gmoccapy/T4-MFA/Fotos/20260506_101403.jpg

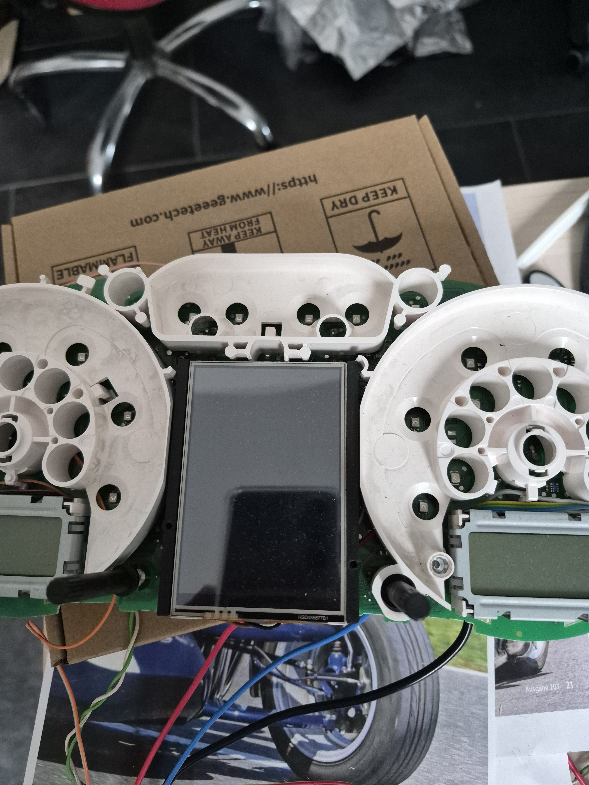
Fotos/20260506_101403.jpg
