gmoccapy/T4-MFA/Fotos/20260506_101413.jpg

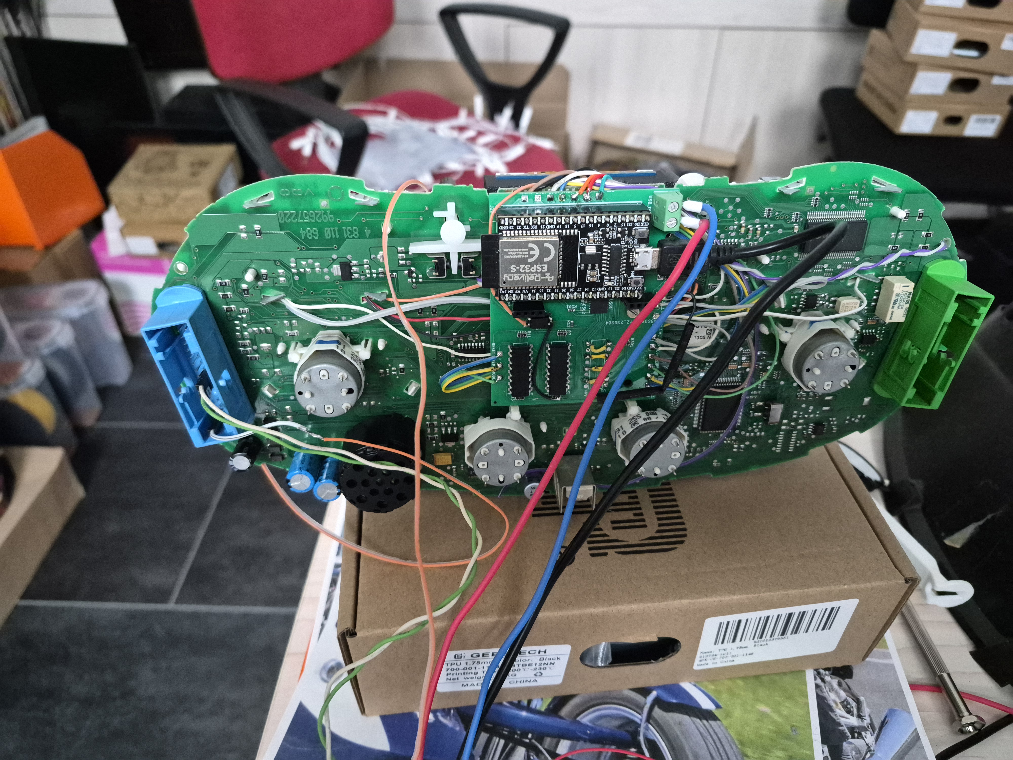
Fotos/20260506_101413.jpg
