gmoccapy/T4-MFA/Fotos/Housing_Power_Suply _ 2.jpg

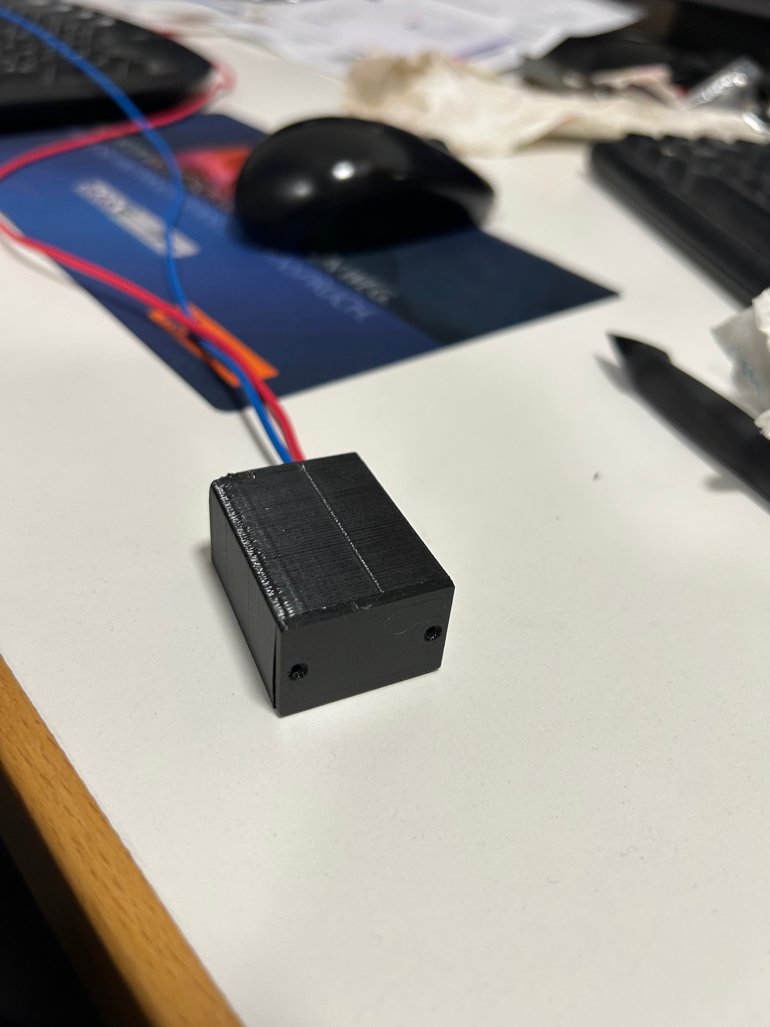
Fotos/Housing_Power_Suply _ 2.jpg
