gmoccapy/T4-MFA/Fotos/Modification_Back_cover_1.jpg

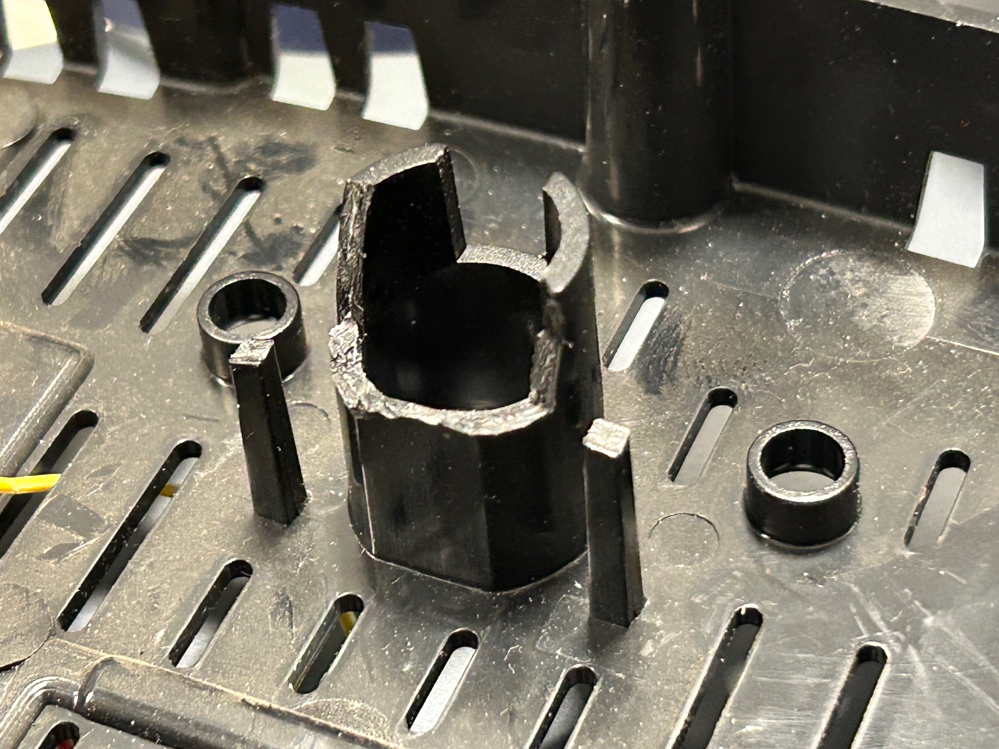
Fotos/Modification_Back_cover_1.jpg
