gmoccapy/T4-MFA/Daniels_Code/MFA_TFT_25012026/update_values.ino

void update_GPS(void) {
    while (GPS_Serial.available() > 0) {
    gps.encode(GPS_Serial.read());
  }
  // gültiges Signal?
  if (gps.location.isValid() && gps.date.isValid() && gps.time.isValid()) {
    _GPS_valid = true;
    
    int hour = gps.time.hour() + _GPS_timezone_offset;
    if (hour >= 24) hour -= 24;
    if (hour < 0) hour += 24;
    _GPS_time = hour * 3600UL + gps.time.minute() * 60UL + gps.time.second();

    _GPS_direction = gps.course.deg();  // 0-360
    _GPS_speed = gps.speed.kmph();
    _GPS_last_update = millis();
    _GPS_altitude = gps.altitude.meters();
  }

  // Timeout: >10 Sekunden dann ungültig
  if (millis() - _GPS_last_update > 10000) {
    _GPS_valid = false;
  }
}

void update_time(void){
  if (motor_on) {         // Zeit für durchschnittsgeschwindigkeit soll nur zählen wenn der Motor läuft
  Data.time_start += ((millis() - lastMillis)) / 1000;
  lastMillis = millis();

 //if (_GPS_valid) {        // GPS Uhrzeit macht hier keinen Sinn, da nur die Zeit genommen werden sollte, wenn der Motor läuft
 //   Data.time_start = _GPS_time;  // Sek. seit Mitternacht
 //   time_last = Data.time_start;
 // }
  // Minuten Logik
  if((Data.time_start - time_last) > 59){
    Data.time_refuel += 1;
    Data.time_long_period += 1;
    time_last = Data.time_start;
  }
  }
  
// DEBUG  
  if(temp_page == 6){
    tft.setTextDatum(MC_DATUM);
   // tft.fillScreen(TFT_BLACK);
    temp = (shutdown_timer + shutdown_time - millis()) / 1000 ;
    dtostrf(temp, 4, 0, TFT_String);
    draw_value_box(250, 134, 50, TFT_String);
  }
}


void update_volt(void){
  // Get the Voltage value from PIN 4 from ESP32 coresponds to ADC1_CH3
  temp = analogRead(PIN_Volt);      
if (temp > 1500) {  // K15 = Zündung an
  ignition_on = true;
} else {
  ignition_on = false;
}

  // Check if over or undervoltage, to turn on the LED

#ifdef SYM_NA_VISIBLE
//kein Batterie Symbol im Display, Batterie wird über getrennte LED im Kombiinstrument angezeigt
#else
if((temp > 4000) || (temp < 1800)){
//    Serial.println(temp);
    if (battery == false) {
      battery = true;
      check_led = true;
    }
  }
  else if(battery == true) {
    battery = false;
    check_led = true;
  }
#endif

  // ignition is on! K15 with 12 V
  if (temp > 1500){
    // ignition came back bevor shut down timer expired, so reset timer
    // and redraw page, as we have blanked it out loosing K15
    if (shutdown_timer != 0){
      shutdown_timer = 0;
      if (temp_page != Data.page){
        temp_page = Data.page;
        DrawSelected(Data.page);
      }
    }
    // if we had an power off, we need to put Hold high
    if (digitalRead(PIN_STAY_ON) == false){
      digitalWrite(PIN_STAY_ON, 1);
    }
  }
  // no Current on K15, so switch off display (better sayed just draw black screen)
  else{
    volt = temp;
    if (motor_on == false){
      if ((shutdown_timer == 0) && (digitalRead(PIN_STAY_ON) == true)){
        shutdown_timer = millis();
        check_led = false;  // otherwise we will have symbols displayed on off page     zusatzprüfung in check_led eingefügt
       temp_page = 6;
       DrawSelected(temp_page);
      }
    }
  }
  // get rid of noise influence ; high pass filtering 
  // take 90% of old value and 10% of new value to smooth the display
  volt = (0.9 * volt) + (0.1 * temp);
}

void update_values(void){
  // max 6 info lines
  // Line 1 = 72
  // Line 2 = 138
  // Line 3 = 204
  // Line 4 = 270
  // Line 5 = 337
  // Line 6 = 404

//DEBUG:
//Serial.println("This is update values");

  tft.setTextDatum(MR_DATUM); // middle right

  // to avoid update values for warnings in full page mode
  if (Data.page == temp_page){
    // Shutdown-Seite (6) unabhängig vom Memory
    if (temp_page == 6) {
      // DEBUG: Countdown aktualisieren
      temp = (shutdown_timer + shutdown_time - millis()) / 1000;
      dtostrf(temp, 4, 0, TFT_String);
      draw_value_box(250, 134, 50, TFT_String);
      return;
    }}

    
    if (currentMemory == 0) {
      switch(Data.page) {
        case 0:
        
          draw_value_cruise_control(70);
          draw_compass(105, 70);
          draw_value_average_consumption(316, Data.mode);
          draw_value_range(372);
          draw_value_out_temp(428);
          // draw oil temp scale
          draw_bar("Oil", "`C", 15, 115, temp_oil, 0, 160, 60, 130, 140);
          // draw volt scale
          draw_bar("V", "V", 269, 115, volt * VOLT_FAKTOR, 0, 18, 11, 15, -1);
          
      #ifdef with_DIAL
      //Serial.println(warnings); 
      if ( (motor_on == false) || (battery)  ){ //    || (warnings)      WARNINGS muss noch geprüftwerden
        // do nothing
      }
      else{
        // draw_dial needs 181 pixel hight, value may be changes with #define SPRITESIZE and SPRITEPIVOT
        switch(Data.mode){

          case START:  
            // C_last_25_km = 1755.65 ml/25km = 70.226 ml/km => 0,070226 l/km = 7.0226 l/100km 
            if (Data.km_start > 0 ){
              // temp = C_last_25_km / 250.0;  // ml/25 km and 100km gives factor 250   
              temp = (Data.C_start / float(Data.km_start)) / 10.0 ; // 1000 ml/l and 100 km gives factor 10
            }
            else{
              temp = 0.0;
            }
              draw_dial(75, 108, temp, 1, C_dial_display_value, 24.0, F("seit"), F("Start"));
            break;

          case REFUEL:
            if (Data.km_start > 0 ){
              temp = (Data.C_refuel / float(Data.km_refuel)) / 10.0 ; // 1000 ml/l and 100 km gives factor 10
            }
            else{
              temp = 0.0;
            }
            draw_dial(75, 108, temp, 1, C_dial_display_value, 24.0, F("seit"), F("Tanken"));
            break;

          case PERIOD:
            if (Data.km_start > 0 ){
              temp = (Data.C_long_period / float(Data.km_long_period)) * 100.0; // l / km *100
            }
            else{
              temp = 0.0;
            }
            draw_dial(75, 108, temp, 1, C_dial_display_value, 24.0, F(""), F("Langzeit"));
            break;
        }
      }
    #endif      



          break;

        case 1:
          draw_value_trip(72,Data.mode);
          draw_value_actual_consumption(138);
          draw_value_deposit(204);
          draw_value_average_consumption(270, Data.mode);
          draw_value_time(337, Data.mode);
          draw_value_average_velocity(404, Data.mode);
          break;

        default:
          break;
      }
    } else {  // Memory == 1
      switch(Data.page) {
        case 0:
   
          break;

        case 1:
      
      draw_value_cruise_control(70);
      draw_compass(105, 70);

      draw_GPS_altitude(70+64);
      draw_GPS_direction(70 + 109); 
      draw_GPS_time(70 + 154);       // Zeile 7
      draw_GPS_speed(70 + 200); 
      draw_value_UMin(337);
      draw_value_oil_temp(404);  
                  
          break;

        default:
          break;
      }
    }
  
}


void clearUnitsArea(int Y_Pos) {    // Bereich löschen zur Umschaltung Verbrauch l/h auf l/100km und zurück

  int h = tft.fontHeight(FONT4);

  int maxWidth = max(
    tft.textWidth(HUNDERTKM, FONT4),
    tft.textWidth(HOUR, FONT4)
  );

  tft.fillRect(
    230,         
    Y_Pos - h,
    maxWidth,
    2 * h,
    BACK_COLOR
  );
}
/*
void draw_value_actual_consumption(int Y_Pos){
  float temp = 0.0;
  // Einheiten dynamisch wechseln: l/h ↔ l/100km
  if (velocity_actual < 5.0) {
    if (units_l_100_km == true) {
      clearUnitsArea(Y_Pos);
      drawUnits(Y_Pos, LITER, HOUR);
      units_l_100_km = false;
    }
    // Stand: zeige l/h
    temp = C_actual_l_per_h;
  } else {
    if (units_l_100_km == false) {
      clearUnitsArea(Y_Pos);
      drawUnits(Y_Pos, LITER, HUNDERTKM);
      units_l_100_km = true;
    }
    // Fahrt: zeige l/100km
    temp = C_actual_l_per_100km;
  }
 
  if (temp > 99.9) temp = 99.9;
  if (temp < 0) temp = 0.0;

  dtostrf(temp, 4, 1, TFT_String);
  draw_value_box(Y_Pos, 134, 50, TFT_String);
}
*/

void draw_value_actual_consumption(int Y_Pos)
{
  float value;

  if (velocity_actual < 5.0f) {
    // l/h
    value = C_actual_l_per_h;
    if (!unit_l_hour) {
      clearUnitsArea(Y_Pos);
      unit_l_hour = true;
    }
    drawUnits(Y_Pos, LITER, HOUR);
  } 
  else {
    // l/100km
    value = C_actual_l_per_100km;
    if (unit_l_hour) {
      clearUnitsArea(Y_Pos);
      unit_l_hour = false;
      }
      drawUnits(Y_Pos, LITER, HUNDERTKM);
  }

  if (value < 0.0f)  value = 0.0f;
  if (value > 99.9f) value = 99.9f;

  dtostrf(value, 4, 1, TFT_String);
  draw_value_box(Y_Pos, 134, 50, TFT_String);
}


void draw_value_time(int Y_Pos, int _case){
  switch(_case){

    case START: // time from start in sec
      temp = Data.time_start;
      break;

    case REFUEL: // time since refuel in min
      temp = Data.time_refuel * 60;
      break;

    case PERIOD: // time long period in min
      temp = Data.time_long_period * 60;
      break;
  }

    // check if we are over 99 hours and 59 minutes
    // if so we have to strip minutes due to space reasons
    if(temp <= 359940){
      char hours[3];
      dtostrf((int(temp) / 3600), 2, 0, hours);
      char minutes[3];
      dtostrf((int(temp) / 60) % 60, 2, 0, minutes);
      // fill with leading zeros
      for(int i = 0; i < strlen(minutes); i++){
        if(minutes[i] == ' '){
          minutes[i] = '0';
        }
        else{
          break;
        }
      }
      strcpy(TFT_String, hours);
      strcat(TFT_String, ":");
      strcat(TFT_String, minutes);
    }
    else{
      dtostrf((int(temp) / 3600), 5, 0, TFT_String);
    } 
    draw_value_box(Y_Pos, 145, 50, TFT_String);
}

void draw_value_trip(int Y_Pos, int _case){
    
    switch(_case){

    case START: // trip from start
      dtostrf(Data.km_start, 3, 0, TFT_String);
      break;
      
    case REFUEL: // trip since refuel
      dtostrf(Data.km_refuel, 3, 0, TFT_String);
      break;
  
    case PERIOD: // trip since refuel
      dtostrf(Data.km_long_period, 6, 0, TFT_String);
      break;
    }
  draw_value_box(Y_Pos, 134, 50, TFT_String);
}

void draw_value_consumption(int Y_Pos, int _case){
  
  switch(_case){

    case START: // consumption from start
      if(Data.C_start > 0){
        // C_from_start = 500 ml  
        temp = Data.C_start / 1000.0; // 1000ml / 1l
        dtostrf(temp, 4, 1, TFT_String);
      }
      else{
        String(F("--.-")).toCharArray(TFT_String, 5);
      }  
      break;

    case REFUEL: // consumption since refuel
      if(Data.C_refuel > 0){
        // C_refuel = 500 ml 
        temp = Data.C_refuel / 1000.0; // 1000ml / 1l
        dtostrf(temp, 4, 1, TFT_String);
      }
      else{
        String(F("--.-")).toCharArray(TFT_String, 5);
      }  
      break;

    case PERIOD: // consumption long period
      if(Data.C_long_period > 0){
        // C_long_period = 86.38 l and km_long_oeriod = 1234 km => 86.38 l * 100.0 km / (1234 km) = 86.38 l / (1234 / 100) km 
        temp = Data.C_long_period; // l
        dtostrf(temp, 4, 1, TFT_String);
      }
      else{
        String(F("--.-")).toCharArray(TFT_String, 5);
      }
      break;  
  }
  draw_value_box(Y_Pos, 134, 50, TFT_String);
}

void draw_value_average_consumption(int Y_Pos, int _case){
  
  switch(_case){

    case START: // average consumption from start
      if(Data.km_start > 0){
        // C_start = 2100 ml and km_start = 35 km => 2100 ml / 35 km => 60 ml / 1 km => 6000 ml / 100 km => 6,0 l / 100 km 
        temp = (Data.C_start / float(Data.km_start)) / 10.0 ; // 1000 ml/l and 100 km gives factor 10
        dtostrf(temp, 4, 1, TFT_String);
      }
      else{
        String(F("--.-")).toCharArray(TFT_String, 5);
      }  
      break;

    case REFUEL: // average consumption since refuel
      if(Data.km_refuel > 0){
        // C_refuel = 2100 ml and km_refuel = 35 km => 2100 ml / 35 km => 60 ml / 1 km => 6000 ml / 100 km => 6,0 l / 100 km 
        temp = (Data.C_refuel / float(Data.km_refuel)) / 10.0 ; // 1000 ml/l and 100 km gives factor 10
        dtostrf(temp, 4, 1, TFT_String);
      }
      else{
        String(F("--.-")).toCharArray(TFT_String, 5);
      }  
      break;

    case PERIOD: // average consumption long period
      if(Data.km_long_period > 0){
        // C_period = 2.100 l and km_period = 35 km => 2.1 l / 35 km => 0.06 l/km => 6.0 l/100 km  
        temp = (Data.C_long_period / float(Data.km_long_period)) * 100.0; // l / km *100
        dtostrf(temp, 4, 1, TFT_String);
      }
      else{
        String(F("--.-")).toCharArray(TFT_String, 5);
      }
      break;  
  }
  draw_value_box(Y_Pos, 134, 50, TFT_String);
}

void draw_value_cruise_control(int Y_Pos){
  // cruise control
  uint color;
  if(velocity_cruise_control > 0){
    dtostrf(velocity_cruise_control, 3, 0, TFT_String);
    color = TFT_GREEN;
  }
  else{
    String(F("---")).toCharArray(TFT_String, 12);
    color = TEXT_COLOR;
  }  
  draw_value_box(Y_Pos, 95, 50, TFT_String); // value box von 134 auf 90 geändert wegen compass
  tft.drawXBitmap(19, Y_Pos - 25, sym_cruise_control, 50, 50, color);
}

void draw_value_average_velocity(int Y_Pos, int _case){
  
  switch(_case){

    case START: // average velocity from start
      if(Data.time_start > 0){
        // time_from_start in sec and km_from_start in km 
        temp = Data.km_start * 3600.0 / float(Data.time_start); 
        dtostrf(temp, 4, 0, TFT_String);
      }
      else{
        String(F("--.-")).toCharArray(TFT_String, 5);
      }  
      break;

    case REFUEL: // average velocity since refuel
      if(Data.time_refuel > 0){
        // km_refuel = 35 km and time_refuel = 57 min => 35 km / 57 min = 0,614 km/min => 0,614 * 60 min/h = 36.8 km/h 
        temp = Data.km_refuel * 60.0 / float(Data.time_refuel); 
        dtostrf(temp, 4, 1, TFT_String);
      }
      else{
        String(F("--.-")).toCharArray(TFT_String, 5);
      }  
      break;

    case PERIOD: // average velocity long period
      if(Data.time_long_period > 0){
        // km_period = 35 km and time_period = 57 min => 35 km / 57 min = 0,614 km/min => 0,614 * 60 min/h = 36.8 km/h 
        temp = Data.km_long_period * 60.0 / float(Data.time_long_period); 
        dtostrf(temp, 4, 1, TFT_String);
      }
      else{
        String(F("--.-")).toCharArray(TFT_String, 5);
      }  
      break;  
  }
  draw_value_box(Y_Pos, 134, 50, TFT_String);
}

void draw_value_oil_temp(int Y_Pos){
  if(temp_oil < 10){
    String(F("---")).toCharArray(TFT_String, 4);
  }
  else{
    dtostrf(temp_oil, 3, 0, TFT_String);
  }
  draw_value_box(Y_Pos, 134, 50, TFT_String);
}

void draw_value_volt(int Y_Pos){
  if(battery == true){
    check_led = true;
    String(F("---")).toCharArray(TFT_String, 4);
  }
  else{
    dtostrf(volt * VOLT_FAKTOR, 6, 1, TFT_String);
  }
  draw_value_box(Y_Pos, 134, 50, TFT_String);
}

void draw_value_out_temp(int Y_Pos){
  dtostrf(temp_out, 6, 1, TFT_String);
  draw_value_box(Y_Pos, 95, 50, TFT_String); //134

bool show_snowflake = (temp_out <= 4.0);

  if (show_snowflake != temp_out_warning) {
      // Hintergrund löschen (einmalig bei Wechsel)
        tft.fillRect(Icon_Pos_Snowflake[0], Icon_Pos_Snowflake[1], 50, 50, BACK_COLOR);
        temp_out_warning = show_snowflake;
  }
       if (show_snowflake) {
            tft.drawXBitmap(Icon_Pos_Snowflake[0], Icon_Pos_Snowflake[1], sym_snowflake, 50, 50, TEXT_COLOR);
        } else {
            tft.drawXBitmap(Icon_Pos_Snowflake[0], Icon_Pos_Snowflake[1], sym_temp2, 50, 50, TEXT_COLOR);
        }
      }

void draw_value_UMin(int Y_Pos){
  static float UMin_smooth = 0.0;
  UMin_smooth = 0.75f * UMin_smooth + 0.25f * UMin; 

  // Runden auf 20er Schritte
  int UMin_display = (int)(UMin_smooth + 10) / 20 * 20;

  if (UMin_display < 0) UMin_display = 0;
  if (UMin_display > 9990) UMin_display = 9990;

  static int last_UMin = -1;
  if (UMin_display != last_UMin) {
    last_UMin = UMin_display;
    dtostrf(UMin_display, 4, 0, TFT_String);
    draw_value_box(Y_Pos, 134, 50, TFT_String);
  }
}

void draw_value_deposit(int Y_Pos){
  dtostrf(deposit, 4, 0, TFT_String);
  draw_value_box(Y_Pos, 134, 50, TFT_String); 
}

void draw_value_range(int Y_Pos){

if (petrol || deposit <= 8) {
    tft.setTextColor(TFT_RED, BACK_COLOR);          
    strcpy(TFT_String, "---");
    draw_value_box(Y_Pos, 134, 50, TFT_String); 
    tft.setTextColor(TEXT_COLOR, BACK_COLOR);  
    return;
  }

  if (Data.km_refuel < 1 || C_last_25_km <= 0.0) {
    String(F("---")).toCharArray(TFT_String, 12);
    draw_value_box(Y_Pos, 134, 50, TFT_String);
    return;
  }

  float verbrauch_ml_pro_km = C_last_25_km / 25.0f;
  float tank_ml = deposit * 1000.0;
  temp = tank_ml / verbrauch_ml_pro_km;

  if (temp > 999) temp = 999;
  if (temp < 0) temp = 0;

  dtostrf(temp, 3, 0, TFT_String);
  draw_value_box(Y_Pos, 134, 50, TFT_String);
}

//Direkte Auswertung des öl level sensor scheint keine brauchbare lösung. besser über K-Line?

//void draw_value_oil_lvl(int Y_Pos) {

//  char buf[12];

//  if (oil_lvl_mm > 0.1f) {
//    dtostrf(oil_lvl_mm, 3, 1, buf);
//    strcat(buf, "mm");                          
  //  Serial.printf(">>> Ölstand: %s\n", buf);    
//  } else {
//    strcpy(buf, "---");
  //  Serial.println(">>> Ölstand: ---");
//  }

//  draw_value_box(Y_Pos, 134, 50, buf);
//}


void draw_GPS_time(int Y_Pos) {
  tft.setTextDatum(ML_DATUM);
  tft.drawString("Zeit", 14, Y_Pos, FONT4);

  if (_GPS_valid) {
    sprintf(TFT_String, "%02lu:%02lu:%02lu",
            _GPS_time / 3600,
            (_GPS_time % 3600) / 60,
            _GPS_time % 60);
  } else {
    strcpy(TFT_String, "!Signal");
  }
  draw_value_box(Y_Pos, 134, 50, TFT_String);
}

void updateDebug(void){
  // DEBUG
  // tft.setTextDatum(MR_DATUM);
  // dtostrf(bitValue[0], 6, 0, TFT_String);
  // draw_value_box(138, 134, 50, TFT_String);
  // dtostrf(bitValue[1], 6, 0, TFT_String);
  // draw_value_box(204, 134, 50, TFT_String);
  // dtostrf(bitValue[2], 6, 0, TFT_String);
  // draw_value_box(270, 134, 50, TFT_String);
  draw_value_cruise_control(404);
  dtostrf(deposit, 6, 0, TFT_String);
  draw_value_box(72, 200, 50, TFT_String);
  // draw_small_value_box(240, 1*24+12, 100, 24, TFT_String);

  // dtostrf(Data.time_start, 6, 0, TFT_String);
  // draw_small_value_box(240, 2*24+12, 100, 24, TFT_String);

  dtostrf(temp_oil, 6, 0, TFT_String);
  draw_value_box(138, 200, 50, TFT_String);
  // draw_small_value_box(240, 3*24+12, 100, 24, TFT_String);

  // dtostrf(Data.km_start, 6, 0, TFT_String);
  // draw_small_value_box(240, 4*24+12, 100, 24, TFT_String);

  dtostrf(C_last_25_km, 8, 0, TFT_String);
  // draw_small_value_box(240, 5*24+12, 100, 24, TFT_String);
  draw_value_box(204, 200, 50, TFT_String);

  // dtostrf(Data.time_refuel, 6, 0, TFT_String);
  // draw_small_value_box(240, 6*24+12, 100, 24, TFT_String);

  dtostrf(UMin, 6, 0, TFT_String);
  // draw_small_value_box(240, 7*24+12, 100, 24, TFT_String);
  draw_value_box(270, 200, 50, TFT_String);

  // dtostrf(velocity_actual, 6, 0, TFT_String);
  // draw_small_value_box(240, 8*24+12, 100, 24, TFT_String);

  // dtostrf(velocity_cruise_control, 6, 0, TFT_String);
  // draw_small_value_box(240, 9*24+12, 100, 24, TFT_String);

  dtostrf(Data.C_last_km, 8, 0, TFT_String);
  // draw_small_value_box(240, 10*24+12, 100, 24, TFT_String);
  draw_value_box(337, 200, 50, TFT_String);

  // dtostrf(Data.C_start, 6, 1, TFT_String);
  // draw_small_value_box(240, 11*24+12, 100, 24, TFT_String);

  // if(velocity_actual > 5){
  //   tft.drawString(F("C_act [l/h]"), 0, 12*24+12, FONT4);
  // }
  // else{
  //   tft.drawString(F("C_act [l/dkm]"), 0, 12*24+12, FONT4);
  // } 
  // dtostrf(C_actual, 4, 4, TFT_String); // calculation l/h or l/100 km is done in read_CAN
  // draw_small_value_box(240, 12*24+12, 100, 24, TFT_String);
}
