gmoccapy/T4-MFA/Daniels_Code/MFA_TFT_25012026/symbols.h

//#define sym_snowflake_width 50
//#define sym_snowflake_height 50
static unsigned char sym_snowflake[] PROGMEM = {
   0x00, 0x00, 0x00, 0x00, 0x00, 0x00, 0x00, 0x00, 0x00, 0x00, 0x00, 0x00,
   0x00, 0x00, 0x00, 0x00, 0x00, 0x03, 0x00, 0x00, 0x00, 0x00, 0x00, 0x80,
   0x07, 0x00, 0x00, 0x00, 0x00, 0x00, 0x80, 0x07, 0x00, 0x00, 0x00, 0x00,
   0x00, 0x8c, 0xc7, 0x00, 0x00, 0x00, 0x00, 0x00, 0x9e, 0xe7, 0x01, 0x00,
   0x00, 0x00, 0x00, 0xbe, 0xf7, 0x01, 0x00, 0x00, 0x00, 0x10, 0xfe, 0xff,
   0x21, 0x00, 0x00, 0x00, 0x38, 0xfc, 0xff, 0x70, 0x00, 0x00, 0x00, 0x7c,
   0xf8, 0x7f, 0xf8, 0x00, 0x00, 0x00, 0x78, 0xf0, 0x3f, 0x78, 0x00, 0x00,
   0x00, 0x78, 0xe0, 0x1f, 0x78, 0x00, 0x00, 0xe0, 0xf9, 0xc0, 0x0f, 0x7c,
   0x1e, 0x00, 0xe0, 0xf7, 0x80, 0x07, 0xbc, 0x1f, 0x00, 0xe0, 0xff, 0x80,
   0x07, 0xfc, 0x1f, 0x00, 0xc0, 0xff, 0x81, 0x07, 0xfe, 0x0f, 0x00, 0x00,
   0xff, 0x81, 0x07, 0xfe, 0x03, 0x00, 0x00, 0xfc, 0x83, 0x07, 0xff, 0x01,
   0x00, 0x80, 0xff, 0x8f, 0xc7, 0xff, 0x07, 0x00, 0xe0, 0xff, 0xbf, 0xe7,
   0xff, 0x1f, 0x00, 0xf0, 0xff, 0xff, 0xff, 0xff, 0x3f, 0x00, 0xf0, 0x1f,
   0xfe, 0xff, 0xe3, 0x3f, 0x00, 0xe0, 0x01, 0xfc, 0xff, 0x00, 0x1e, 0x00,
   0x00, 0x00, 0xf0, 0x3f, 0x00, 0x00, 0x00, 0x00, 0x00, 0xf0, 0x3f, 0x00,
   0x00, 0x00, 0xe0, 0x01, 0xfc, 0xff, 0x00, 0x1e, 0x00, 0xf0, 0x1f, 0xfe,
   0xff, 0xe3, 0x3f, 0x00, 0xf0, 0xff, 0xff, 0xff, 0xff, 0x3f, 0x00, 0xe0,
   0xff, 0x9f, 0xe7, 0xff, 0x1f, 0x00, 0x80, 0xff, 0x8f, 0xc7, 0xff, 0x07,
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
	0x0f, 0x7e, 0x00, 0x00, 0x00, 0xf0, 0x80, 0x07, 0x3c, 0x00, 0x00, 0x00, 0xf0, 0x80, 0x07, 0x3c, 
	0x00, 0x00, 0x00, 0x60, 0x00, 0x03, 0x18, 0x00, 0x00, 0x00, 0x60, 0x00, 0x03, 0x18, 0x00, 0x00, 
	0x00, 0x00, 0x00, 0x00, 0x00, 0x00, 0x00, 0x00, 0x00, 0x00, 0x00, 0x00, 0x00, 0x00
};
