gmoccapy/T4-MFA/Daniels_Code/Daniel/doors_sprite_1/doors.ino

//
//Türen und Klappen zählen wie folgt: Fahrertür = 1; Beifahrertür = 2; Schiebetür = 4; Heckklappe = 8; Motorhaube = 16
//Fahrertür und Heckklappe offen -> 1 + 8 = 9 --> door_9
//Fahrertür, Beifahrertür und Schiebetür offen-> 1 + 2 + 4 = 7 
//Motorhaube + Schiebetür offen -> 16 + 4 = 20 --> door_20

void door_0(void){
  d_spr.createSprite (170,350);
  d_spr.fillSprite(TFT_BLACK);
  d_spr.drawXBitmap(0, 0, d_T4, 170, 350,TFT_WHITE);
  d_spr.drawXBitmap(0, 0, d_fl_c, 170, 350,TFT_WHITE);
  d_spr.drawXBitmap(0, 0, d_fr_c, 170, 350,TFT_WHITE);
  d_spr.drawXBitmap(0, 0, d_sd_c, 170, 350,TFT_WHITE);
  d_spr.drawXBitmap(0, 0, d_t_c, 170, 350,TFT_WHITE);
  d_spr.pushSprite(75,65);
  d_spr.deleteSprite();
};  

void door_1(void){
  d_spr.createSprite (170,350);
  d_spr.fillSprite(TFT_BLACK);
  d_spr.drawXBitmap(0, 0, d_T4, 170, 350,TFT_WHITE);
  d_spr.drawXBitmap(0, 0, d_fl_o, 170, 350,TFT_RED);
  d_spr.drawXBitmap(0, 0, d_fr_c, 170, 350,TFT_WHITE);
  d_spr.drawXBitmap(0, 0, d_sd_c, 170, 350,TFT_WHITE);
  d_spr.drawXBitmap(0, 0, d_t_c, 170, 350,TFT_WHITE);
  d_spr.pushSprite(75,65);
  d_spr.deleteSprite();
};  

void door_2(void){
  d_spr.createSprite (170,350);
  d_spr.fillSprite(TFT_BLACK);
  d_spr.drawXBitmap(0, 0, d_T4, 170, 350,TFT_WHITE);
  d_spr.drawXBitmap(0, 0, d_fl_c, 170, 350,TFT_WHITE);
  d_spr.drawXBitmap(0, 0, d_fr_o, 170, 350,TFT_RED);
  d_spr.drawXBitmap(0, 0, d_sd_c, 170, 350,TFT_WHITE);
  d_spr.drawXBitmap(0, 0, d_t_c, 170, 350,TFT_WHITE);
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
  d_spr.drawXBitmap(0, 0, d_fr_o, 170, 350,TFT_RED);
  d_spr.drawXBitmap(0, 0, d_sd_o, 170, 350,TFT_RED);
  d_spr.drawXBitmap(0, 0, d_t_o, 170, 350,TFT_RED);
  d_spr.drawXBitmap(0, 0, d_hood_o, 170, 350,TFT_RED);
  d_spr.pushSprite(75,65);
  d_spr.deleteSprite();
};  

void door_31(void){
  d_spr.createSprite (170,350);
  d_spr.fillSprite(TFT_BLACK);
  d_spr.drawXBitmap(0, 0, d_T4_t_o, 170, 350,TFT_WHITE);
  d_spr.drawXBitmap(0, 0, d_fl_o, 170, 350,TFT_RED);
  d_spr.drawXBitmap(0, 0, d_fr_o, 170, 350,TFT_RED);
  d_spr.drawXBitmap(0, 0, d_sd_o, 170, 350,TFT_RED);
  d_spr.drawXBitmap(0, 0, d_t_o, 170, 350,TFT_RED);
  d_spr.drawXBitmap(0, 0, d_hood_o, 170, 350,TFT_RED);
  d_spr.pushSprite(75,65);
  d_spr.deleteSprite();
}; 
