gmoccapy/T4-MFA/Daniels_Code/Daniel/doors_sprite_2/sym_door.h

 // 'd_l_c', 15x54px
const unsigned char d_l_c [] PROGMEM = {
	0x80, 0x01, 0x80, 0x02, 0x80, 0x02, 0x80, 0x04, 0x80, 0x04, 0x80, 0x04, 0x80, 0x04, 0x80, 0x0c, 
	0x00, 0x0a, 0x00, 0x0a, 0x00, 0x0a, 0x80, 0x07, 0xc0, 0x17, 0xe0, 0x16, 0x98, 0x1f, 0xc4, 0x1f, 
	0xe2, 0x02, 0xf1, 0x02, 0x8d, 0x22, 0x83, 0x22, 0x80, 0x22, 0x80, 0x22, 0x80, 0x22, 0x80, 0x22, 
	0x80, 0x02, 0x80, 0x02, 0x80, 0x02, 0x80, 0x02, 0x80, 0x42, 0x80, 0x42, 0x80, 0x42, 0x80, 0x42, 
	0x80, 0x42, 0x80, 0x42, 0x80, 0x42, 0x80, 0x42, 0x80, 0x42, 0x80, 0x42, 0x80, 0x42, 0x80, 0x42, 
	0x80, 0x42, 0x80, 0x42, 0x80, 0x42, 0x00, 0x42, 0x00, 0x42, 0x00, 0x42, 0x00, 0x42, 0x00, 0x42, 
	0x00, 0x4c, 0x00, 0x58, 0x00, 0x60, 0x00, 0x40, 0x80, 0x40, 0x80, 0x7f
};

// 'd_r_c', 17x54px
const unsigned char d_r_c [] PROGMEM = {
	0x80, 0x01, 0x00, 0x40, 0x01, 0x00, 0x20, 0x01, 0x00, 0x20, 0x01, 0x00, 0x30, 0x01, 0x00, 0x30, 
	0x01, 0x00, 0x30, 0x01, 0x00, 0x38, 0x01, 0x00, 0x28, 0x01, 0x00, 0x28, 0x01, 0x00, 0x28, 0x01, 
	0x00, 0xe8, 0x01, 0x00, 0x6c, 0x03, 0x00, 0x6c, 0x0f, 0x00, 0xfc, 0x31, 0x00, 0xe4, 0x43, 0x00, 
	0x64, 0x87, 0x00, 0x64, 0x1b, 0x01, 0x62, 0xe3, 0x01, 0x62, 0x83, 0x01, 0x62, 0x03, 0x00, 0x62, 
	0x03, 0x00, 0x62, 0x03, 0x00, 0x62, 0x01, 0x00, 0x62, 0x01, 0x00, 0x42, 0x01, 0x00, 0x42, 0x01, 
	0x00, 0x40, 0x01, 0x00, 0x40, 0x01, 0x00, 0x40, 0x01, 0x00, 0x41, 0x01, 0x00, 0x41, 0x01, 0x00, 
	0x41, 0x01, 0x00, 0x41, 0x01, 0x00, 0x41, 0x01, 0x00, 0x41, 0x01, 0x00, 0x41, 0x01, 0x00, 0x41, 
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
	0x00, 0x00, 0x00, 0x00, 0x00, 0x00, 0x00, 0x00, 0x00, 0x00, 0x00, 0x00, 0x00, 0x00, 0x00, 0x00, 
	0x00, 0x00, 0x00, 0x00, 0x00, 0x00, 0x00, 0x00, 0x00, 0x00, 0x00, 0x00, 0x00, 0x00, 0x00, 0x00, 
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
};
