gmoccapy/T4-MFA/Daniels_Code/MFA_TFT_25012026/IO_handling.ino

void check_IO(){ // int PIN, bool mcp_state){


// DEBUG : There shoud never be print statements on interupt routines!
//         We need to delete them at the end of testing
  warnings = 0;

  // as we do not use MCP PINS 14 and 15 we only iterate to 13
  // as MCP PIN 11 ; 12 and 13 are handling the control button, we will handle them separate
  for (byte i = 0; i < 11; i++){
    // MCP PIN 6 and 7 are not used
    if ((i == 6) || (i == 7)){
      continue;
    }
    if (mcp.digitalRead(i) == true){
      warnings += pow(2, i);
//      Serial.println(i);
    }
  }

  // this is the control button handling
  for (byte i = 11; i < 14; i++){
    switch (i){

      // Mode button
   case 11:
  if (mcp.digitalRead(i) == true) {  
    if (Mode_Button_pressed == 0) {
      Mode_Button_pressed = millis();
    }
  } else {  // LOSGELASSEN
    if (Mode_Button_pressed != 0) {
      unsigned long hold_time = millis() - Mode_Button_pressed;

      if (hold_time > 1000) {
        switch_page();
      }
      else if (hold_time > 100) {
        Data.mode +=1;
        if (Data.mode > 3){
          Data.mode = 1;
        }
        //Data.mode = (Data.mode + 1) % 3;
        DrawSelected(Data.page);
      }
      // else: ignorieren

      Mode_Button_pressed = 0;
    }
  }
  break;

// ToDo : Implement memory button ; will switch between setup and operation
      // Memory button
      case 12:
        if (mcp.digitalRead(i) == true){
          //Serial.println("Memory Button");
        //  Memory_Button_pressed = millis();
          Memory_Button_state = true;
        }
         else{
           Memory_Button_state = false;
        }
        break;

      // Reset button
      case 13:
        if (mcp.digitalRead(i) == true){
          Reset_Button_pressed = millis();
          //Serial.println("Reset Button");
        }
        else{
          Reset_Button_pressed = 0;
        }
        break;
    }
  }

  // Serial.print("warnings = ");
  // Serial.println(warnings);

  check_led = true;

  mcp.clearInterrupts();  // clear
  PIN_INT_state = true;
}
