gmoccapy/T4-MFA/Fotos/20260506_101406.jpg

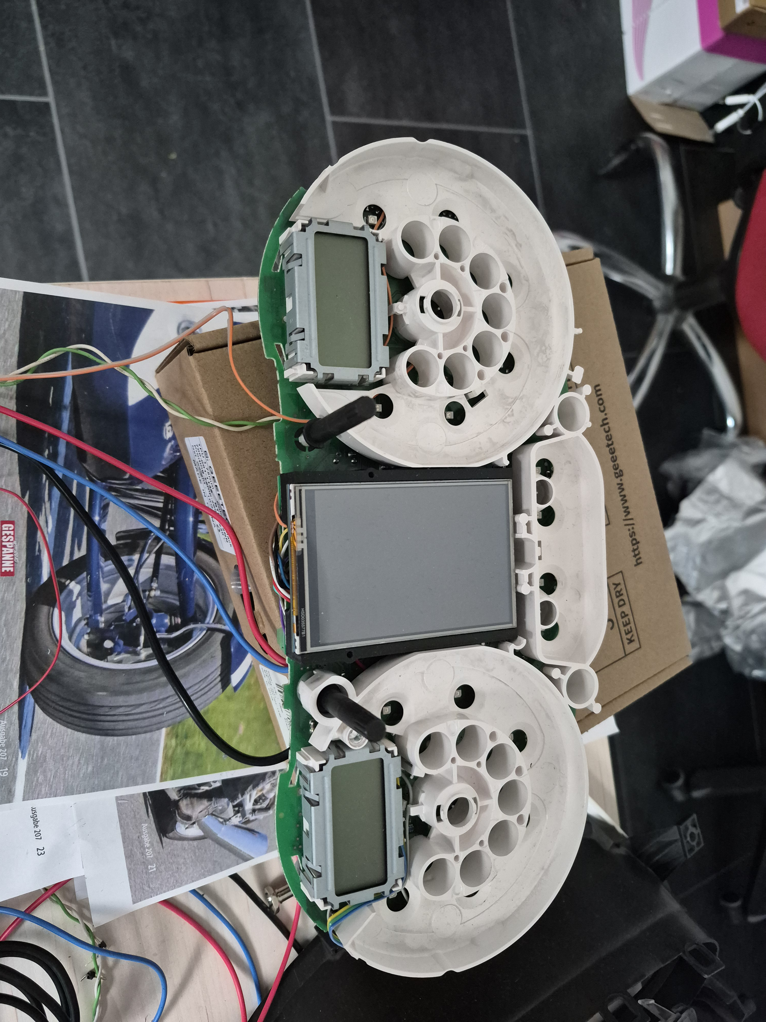
Fotos/20260506_101406.jpg
